Praka245/CUSTOM-ESP32-BOARD/IMAGES/PCB Layout/L2.png

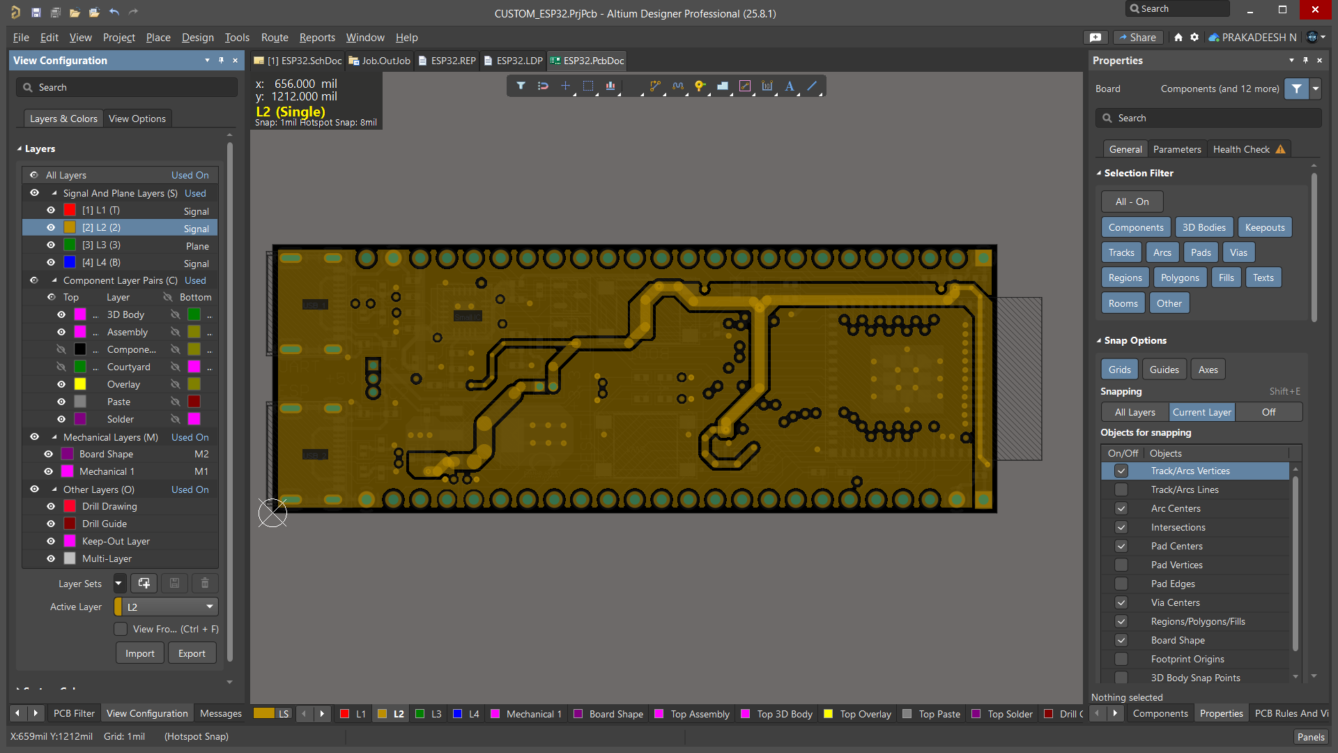
IMAGES/PCB Layout/L2.png
