Praka245/CUSTOM-ESP32-BOARD/IMAGES/PCB Layout/Layout.png

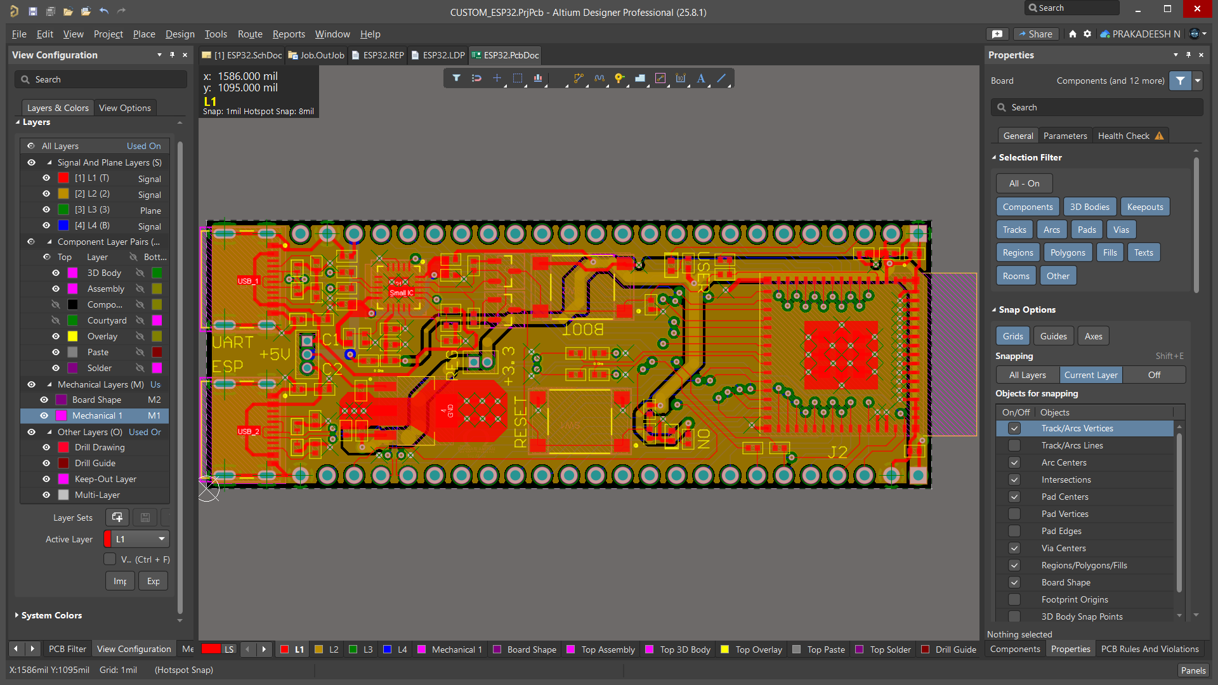
IMAGES/PCB Layout/Layout.png
