Praka245/CUSTOM-ESP32-BOARD/IMAGES/STACK LAYER/Layer Stackup.png

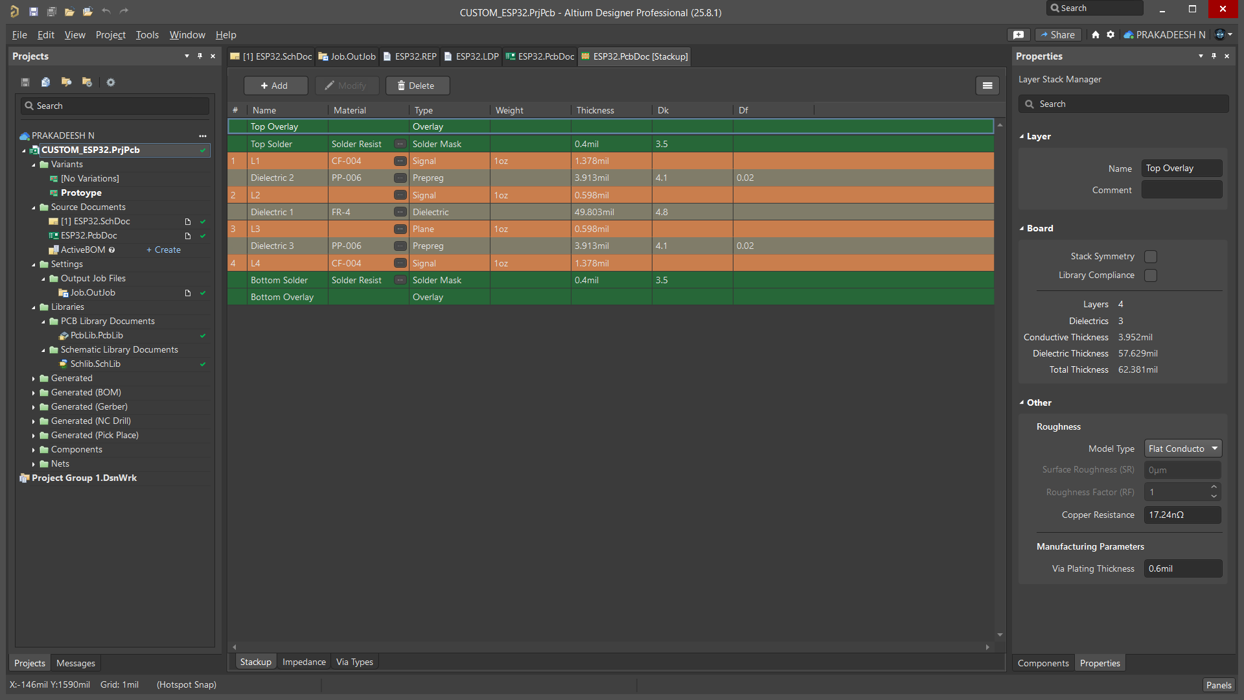
IMAGES/STACK LAYER/Layer Stackup.png
